robandwend/rook-180-extended/UserMods/RobandWend/12864DisplayFront/image1.JPG

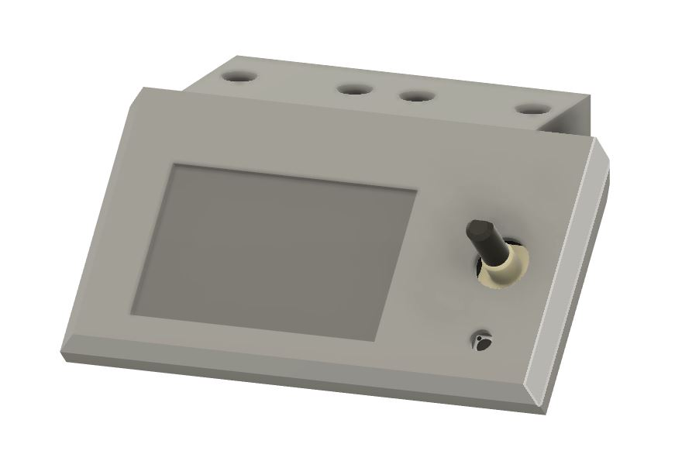
UserMods/RobandWend/12864DisplayFront/image1.JPG
