robandwend/rook-180-extended/UserMods/RobandWend/12864DisplayFront/image2.JPG

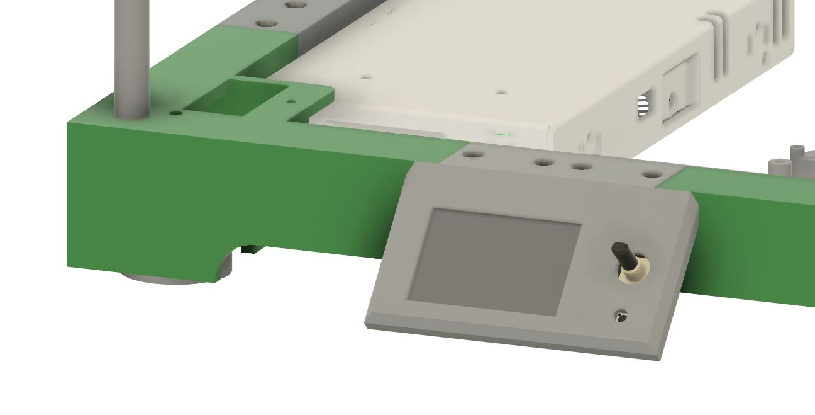
UserMods/RobandWend/12864DisplayFront/image2.JPG
