robandwend/rook-180-extended/UserMods/RobandWend/Photos/ClipGrabPoints.JPG

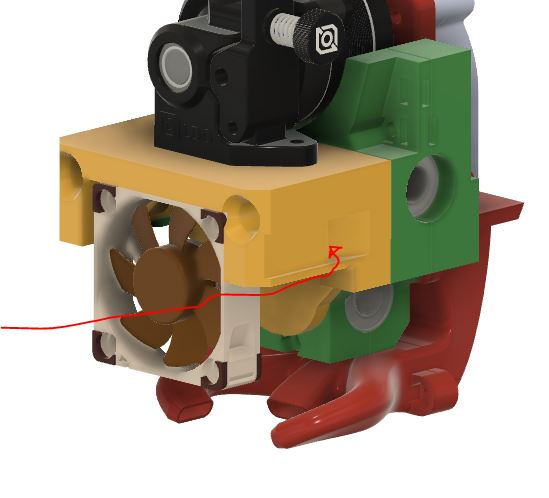
UserMods/RobandWend/Photos/ClipGrabPoints.JPG
