robandwend/rook-180-extended/UserMods/RobandWend/Multi_Hotend/STL/ReplacementArmPart1.stl

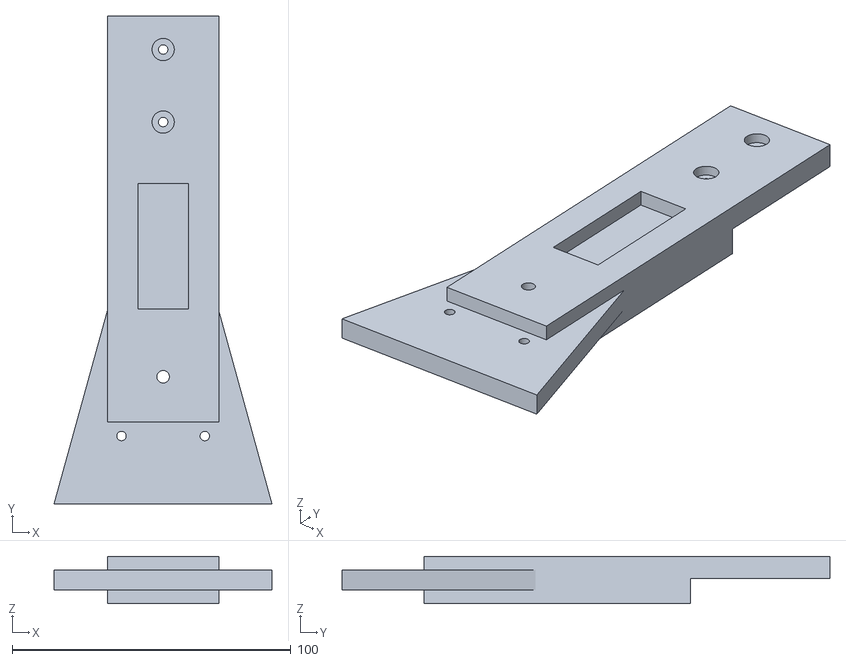
[picture p39: CAD file, 2023-02-05]
UserMods/RobandWend/Multi_Hotend/STL/ReplacementArmPart1.stl
78.1 x 174.9 x 17.0
