robandwend/rook-180-extended/UserMods/RobandWend/Planetery Gear/cover.stl

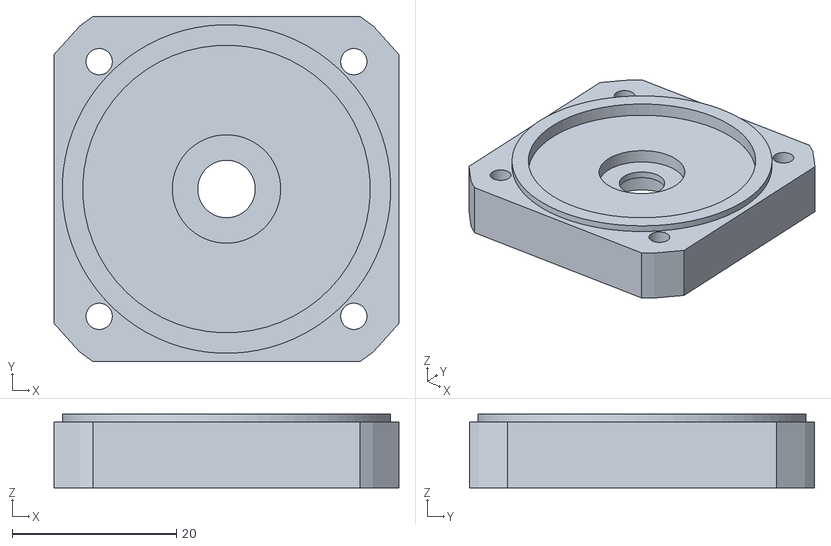
[picture p40: CAD file, 2023-02-15]
UserMods/RobandWend/Planetery Gear/cover.stl
42.0 x 42.0 x 9.00
