robandwend/rook-180-extended/UserMods/RobandWend/Steps/OrbiterWireMount.stl

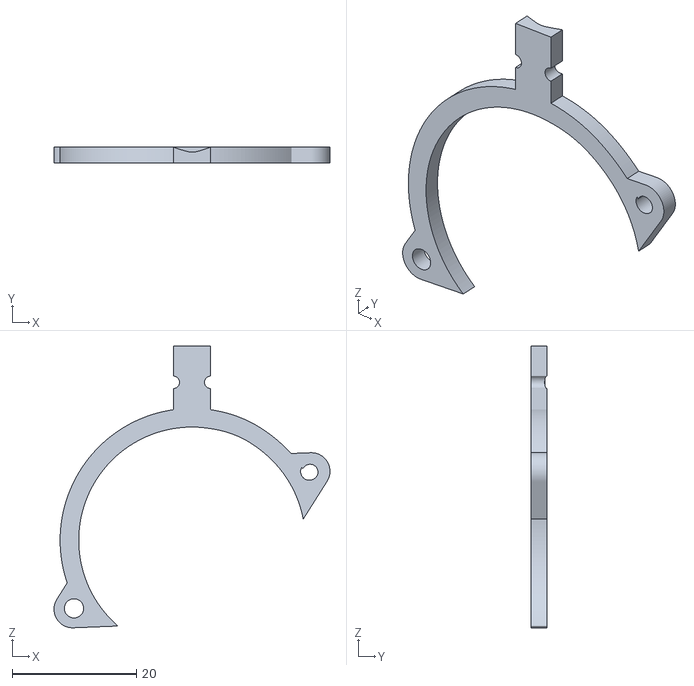
[picture p41: CAD file, 2023-03-21]
UserMods/RobandWend/Steps/OrbiterWireMount.stl
44.4 x 2.50 x 45.3
