robandwend/rook-180-extended/UserMods/RobandWend/Planetery Gear/sun.stl

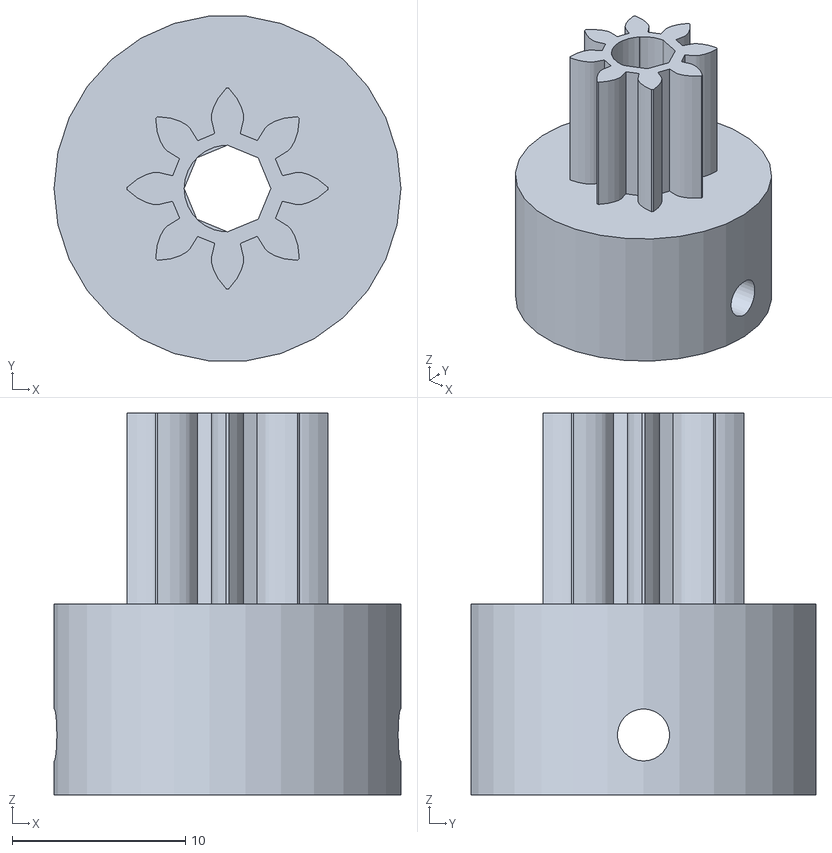
[picture p42: CAD file, 2023-02-15]
UserMods/RobandWend/Planetery Gear/sun.stl
20.0 x 19.9 x 22.0
