robandwend/rook-180-extended/UserMods/RobandWend/Steps/Brace with Raspberry Pi.stl

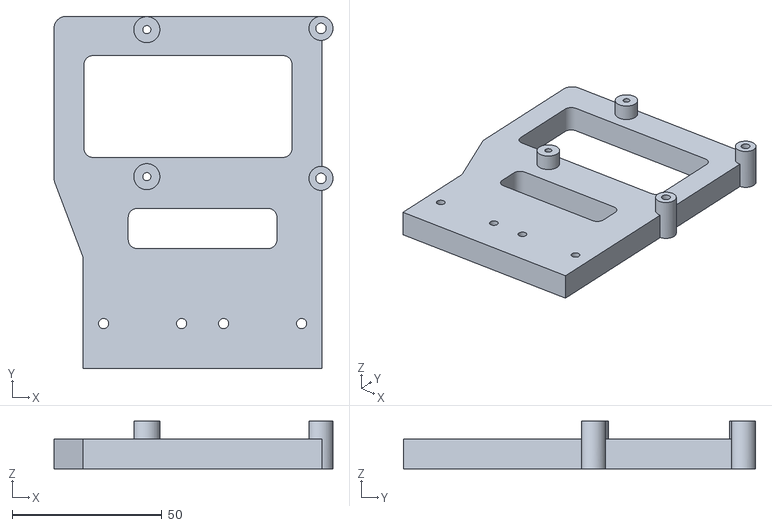
[picture p43: CAD file, 2023-03-21]
UserMods/RobandWend/Steps/Brace with Raspberry Pi.stl
93.0 x 117.4 x 16.0
