robandwend/rook-180-extended/UserMods/RobandWend/Multi_Hotend/STL/2xBottomExtension.stl

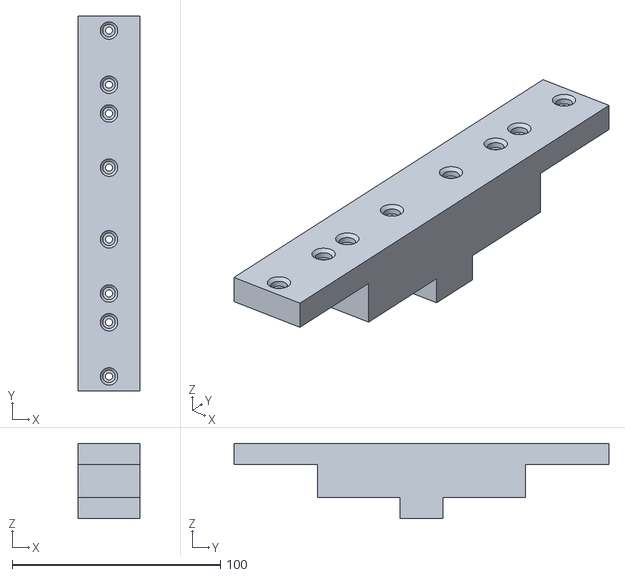
[picture p44: CAD file, 2023-02-05]
UserMods/RobandWend/Multi_Hotend/STL/2xBottomExtension.stl
30.0 x 180.0 x 36.1
