robandwend/rook-180-extended/UserMods/RobandWend/Planetery Gear/planet.stl

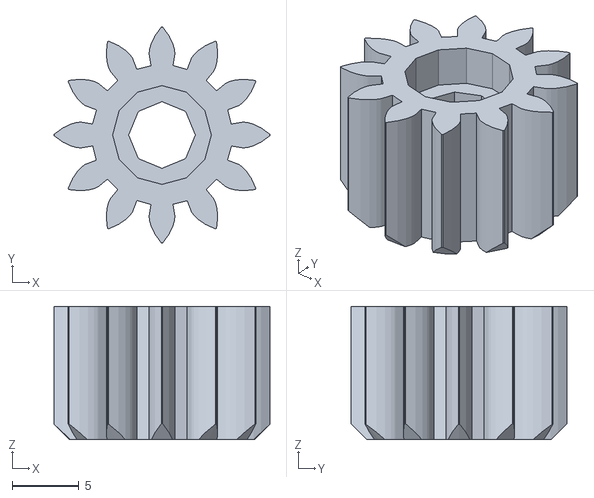
[picture p45: CAD file, 2023-02-15]
UserMods/RobandWend/Planetery Gear/planet.stl
16.2 x 16.2 x 10.0
