robandwend/rook-180-extended/UserMods/RobandWend/Steps/ServoHanger.stl

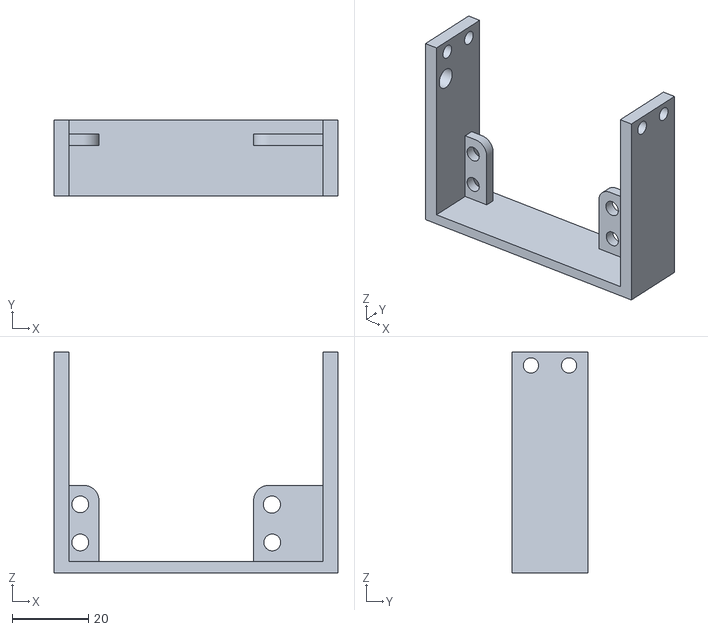
[picture p46: CAD file, 2023-03-21]
UserMods/RobandWend/Steps/ServoHanger.stl
74.6 x 20.0 x 58.0
