robandwend/rook-180-extended/UserMods/RobandWend/Multi_Hotend/STL/2xTopExtension.stl

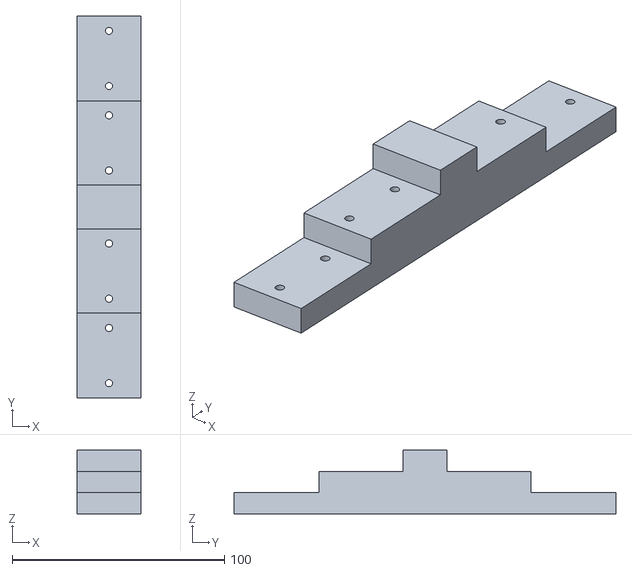
[picture p47: CAD file, 2023-02-05]
UserMods/RobandWend/Multi_Hotend/STL/2xTopExtension.stl
30.0 x 180.0 x 30.0
