robandwend/rook-180-extended/UserMods/RobandWend/Planetery Gear/carrier.stl

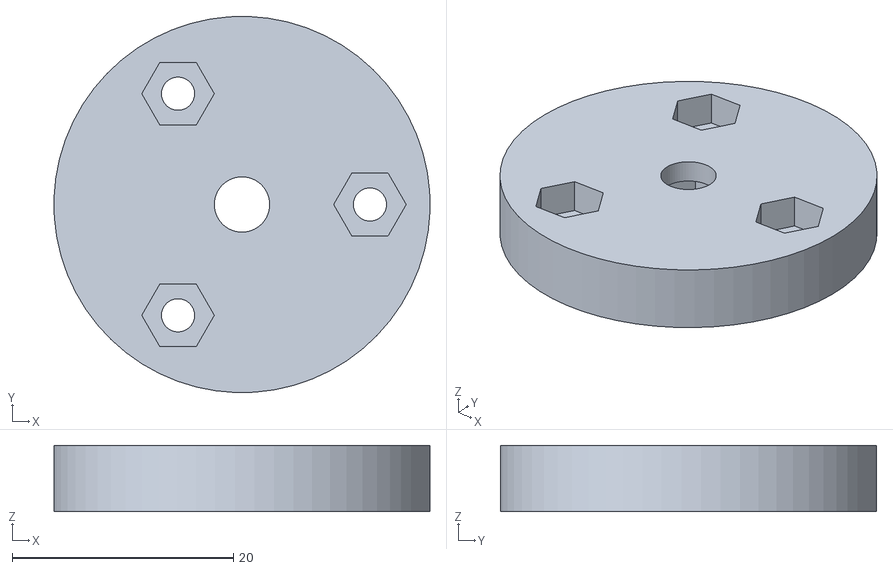
[picture p48: CAD file, 2023-02-15]
UserMods/RobandWend/Planetery Gear/carrier.stl
34.0 x 34.0 x 6.00
