robandwend/rook-180-extended/UserMods/RobandWend/Steps/GrabberHousing.stl

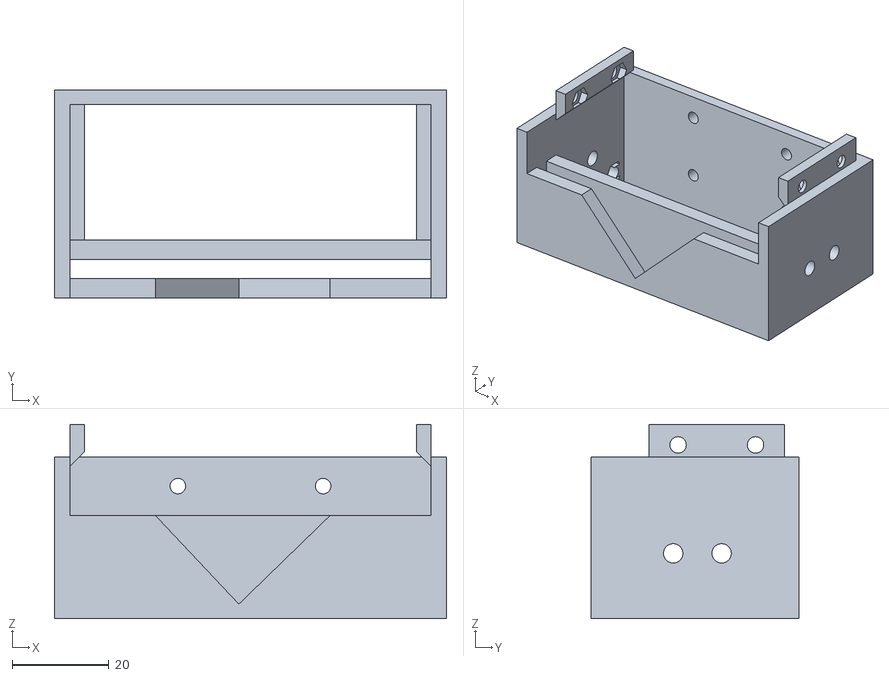
[picture p49: CAD file, 2023-03-21]
UserMods/RobandWend/Steps/GrabberHousing.stl
81.0 x 43.0 x 40.1
