robandwend/rook-180-extended/UserMods/RobandWend/Steps/HorseShoeBrace200mm.stl

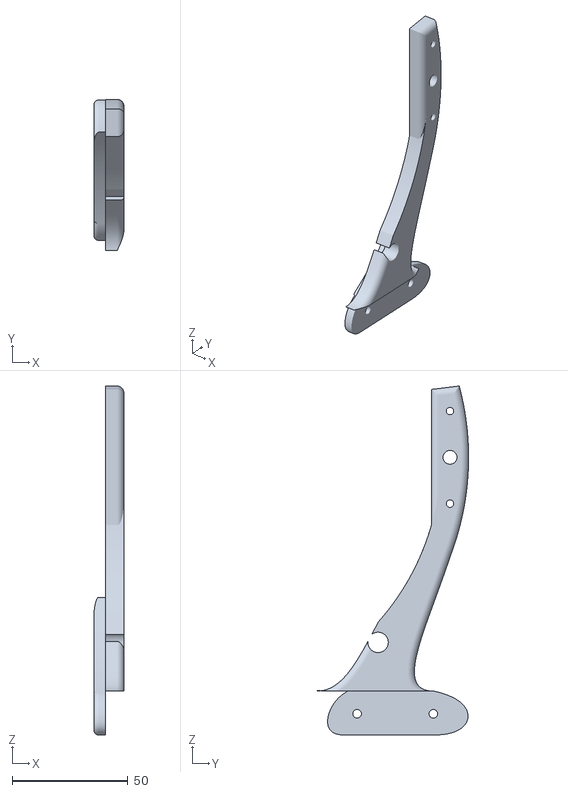
[picture p50: CAD file, 2023-03-21]
UserMods/RobandWend/Steps/HorseShoeBrace200mm.stl
13.0 x 65.3 x 150.7
