robandwend/rook-180-extended/UserMods/RobandWend/Steps/TopServoMount.stl

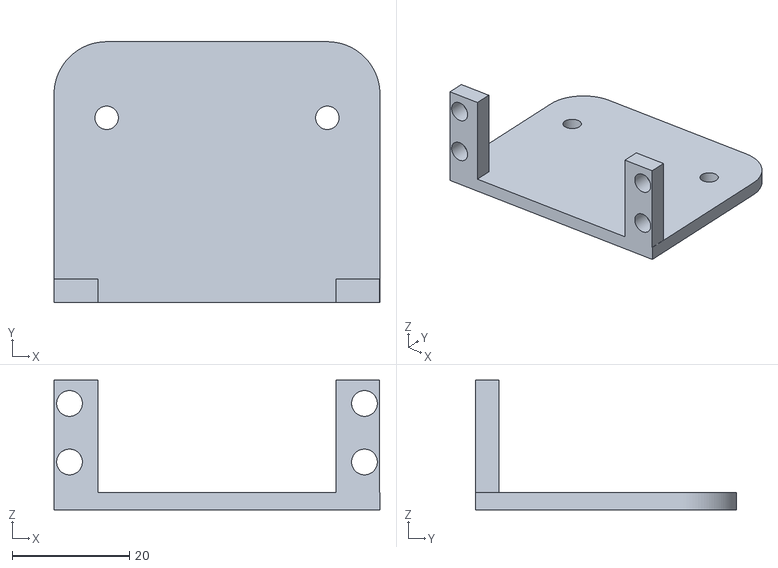
[picture p51: CAD file, 2023-03-21]
UserMods/RobandWend/Steps/TopServoMount.stl
55.7 x 44.5 x 22.2
