robandwend/rook-180-extended/UserMods/RobandWend/Steps/5050 TO 4040 Fan Converter.stl

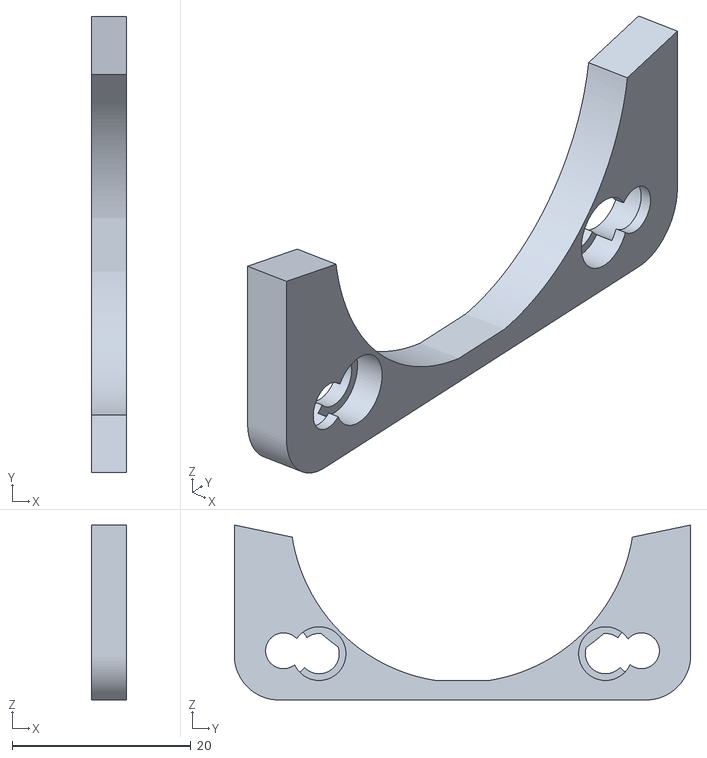
[picture p52: CAD file, 2023-03-21]
UserMods/RobandWend/Steps/5050 TO 4040 Fan Converter.stl
3.95 x 51.0 x 19.6
