robandwend/rook-180-extended/UserMods/RobandWend/Steps/5015_Adapter.stl

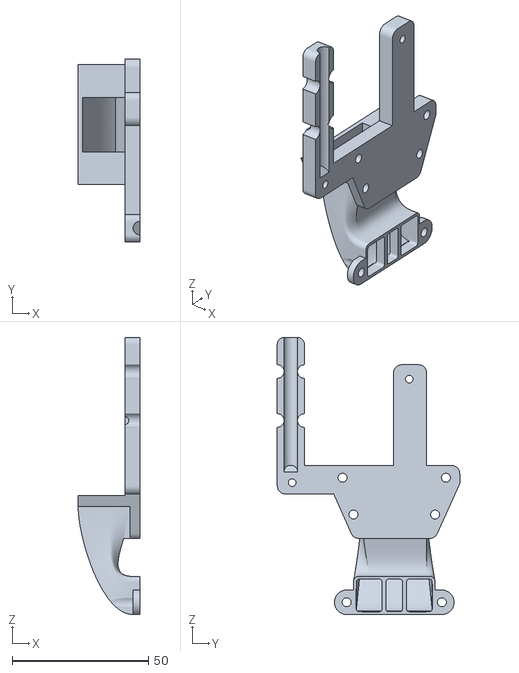
[picture p53: CAD file, 2023-03-21]
UserMods/RobandWend/Steps/5015_Adapter.stl
22.7 x 67.1 x 101.8
