robandwend/rook-180-extended/UserMods/RobandWend/Steps/ExternalSpoolHolder-95mm.stl

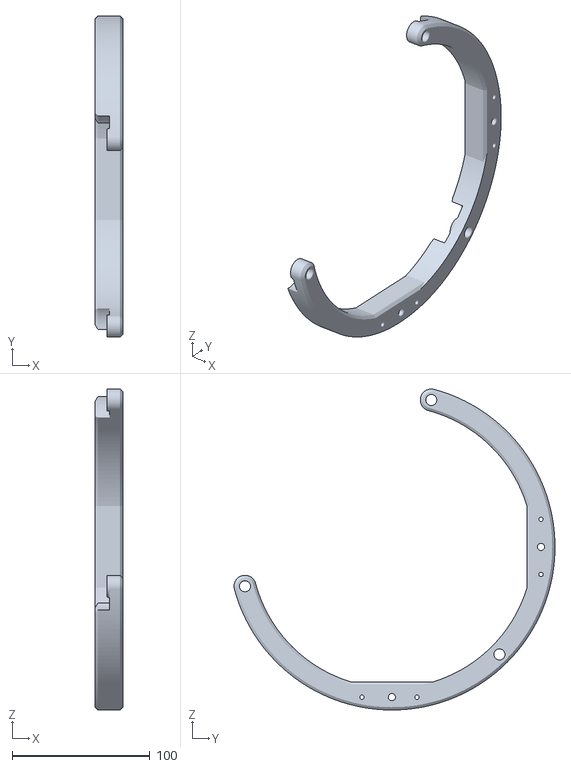
[picture p54: CAD file, 2023-03-21]
UserMods/RobandWend/Steps/ExternalSpoolHolder-95mm.stl
20.0 x 233.2 x 233.2
