robandwend/rook-180-extended/UserMods/RobandWend/Steps/BLTouchStrengthener.stl

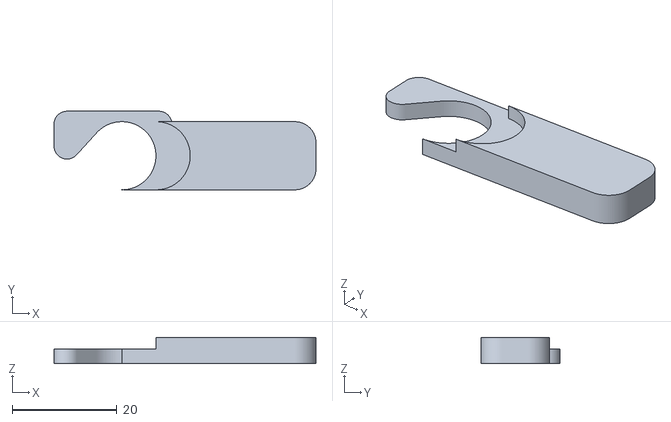
[picture p55: CAD file, 2023-03-21]
UserMods/RobandWend/Steps/BLTouchStrengthener.stl
50.0 x 15.0 x 5.00
