robandwend/rook-180-extended/UserMods/RobandWend/Steps/Z-Endstop.stp

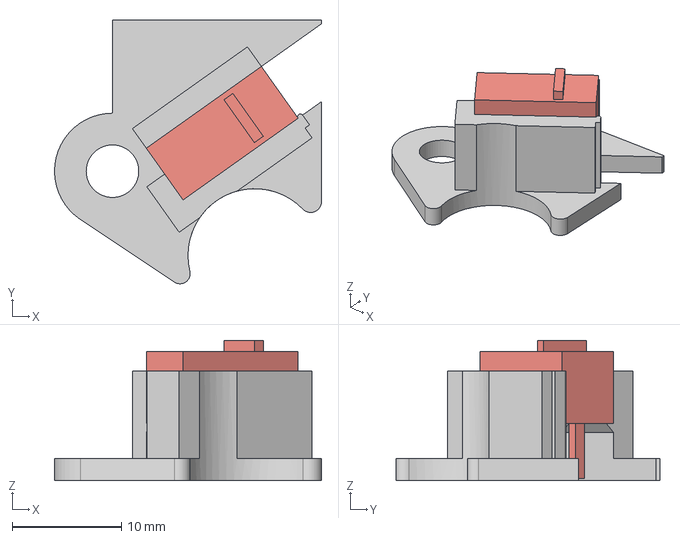
[picture p56: CAD file, 2023-03-21]
UserMods/RobandWend/Steps/Z-Endstop.stp
24.4 x 24.1 x 12.8 mm
