robandwend/rook-180-extended/UserMods/RobandWend/Steps/HarnessClip.stl

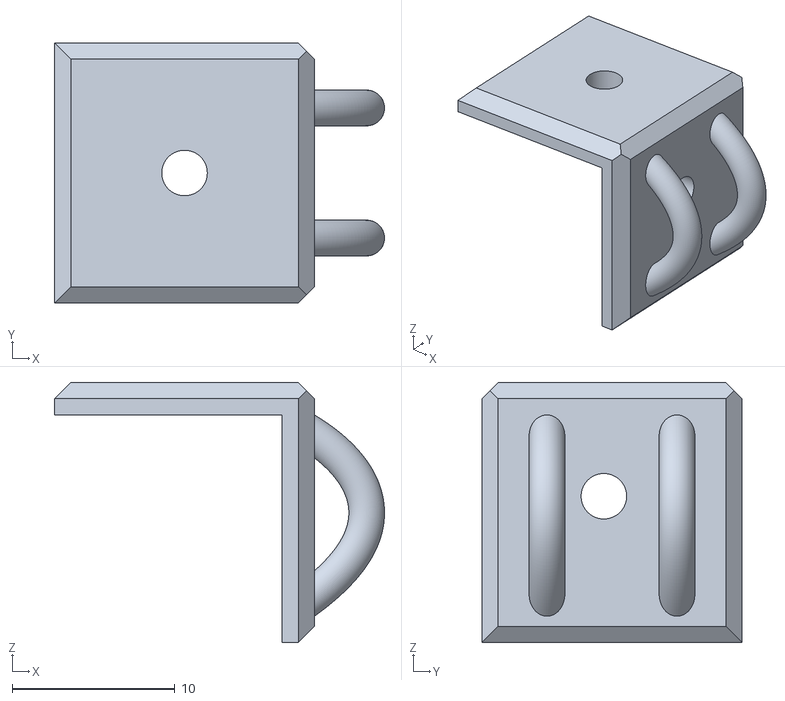
[picture p57: CAD file, 2023-03-21]
UserMods/RobandWend/Steps/HarnessClip.stl
20.3 x 16.0 x 16.0
