robandwend/rook-180-extended/UserMods/RobandWend/Steps/PushOpenBarWithPullback (HB Harness room).stl

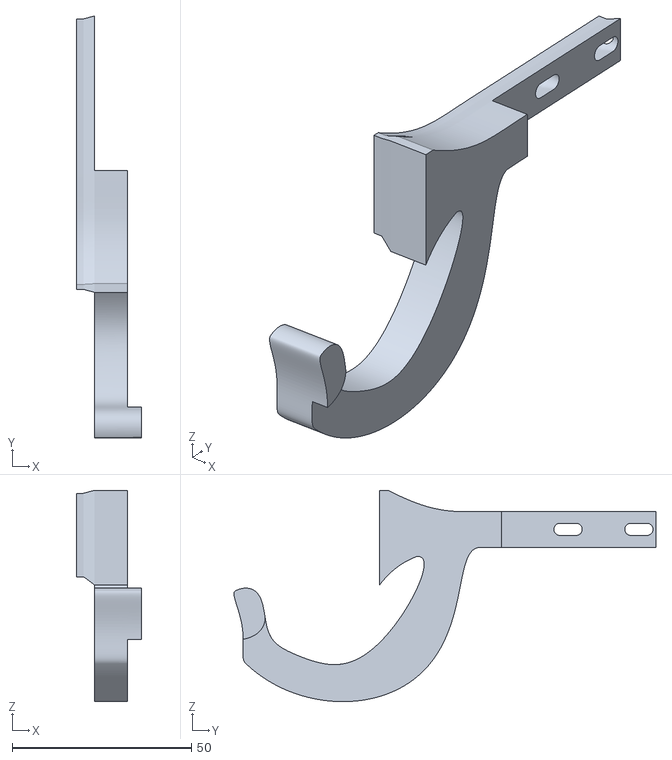
[picture p58: CAD file, 2023-03-21]
UserMods/RobandWend/Steps/PushOpenBarWithPullback (HB Harness room).stl
18.2 x 117.6 x 58.9
