robandwend/rook-180-extended/UserMods/RobandWend/Steps/GrabberHanger(0).stl

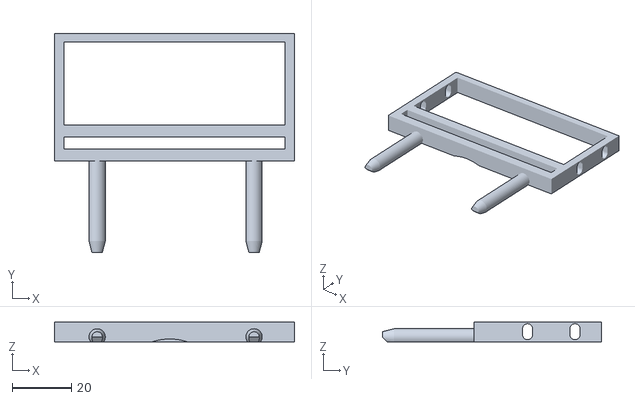
[picture p59: CAD file, 2023-02-15]
UserMods/RobandWend/Steps/GrabberHanger(0).stl
81.0 x 74.0 x 6.70
