robandwend/rook-180-extended/UserMods/RobandWend/Steps/Grabbers.stl

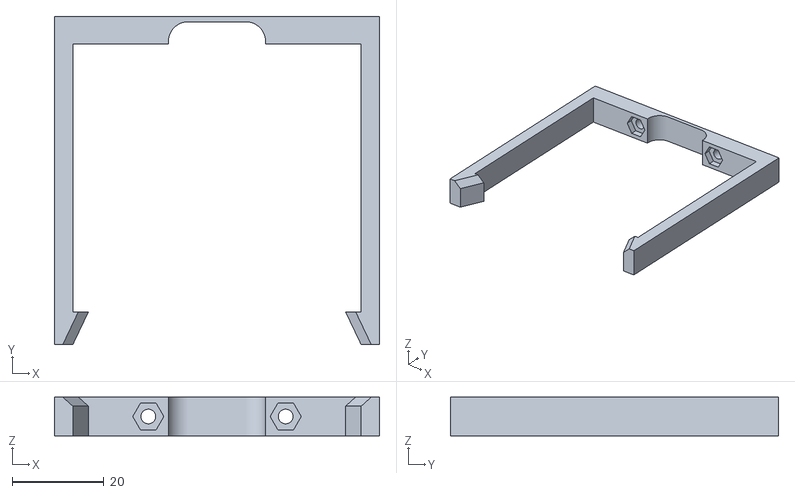
[picture p60: CAD file, 2023-02-15]
UserMods/RobandWend/Steps/Grabbers.stl
71.0 x 71.7 x 8.50
