robandwend/rook-180-extended/UserMods/RobandWend/Steps/ExtruderMount.stl

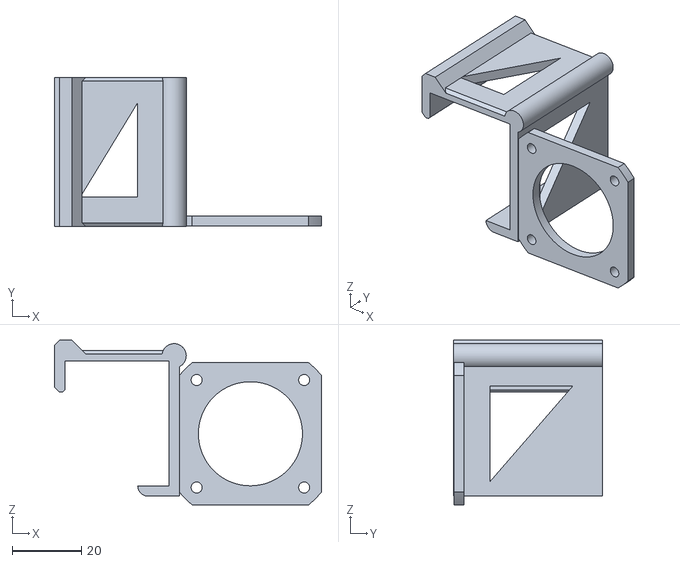
[picture p61: CAD file, 2023-02-15]
UserMods/RobandWend/Steps/ExtruderMount.stl
77.0 x 43.0 x 47.5
