robandwend/rook-180-extended/UserMods/RobandWend/Steps/GrabberTest1.stl

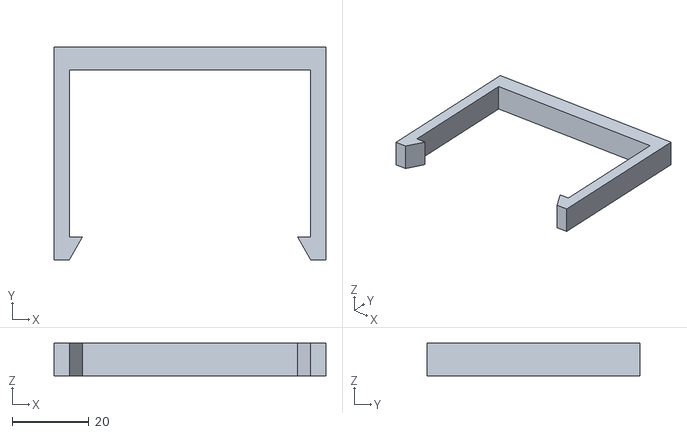
[picture p62: CAD file, 2023-02-15]
UserMods/RobandWend/Steps/GrabberTest1.stl
71.0 x 55.5 x 8.50
