robandwend/rook-180-extended/UserMods/RobandWend/Steps/FrontPart.stl

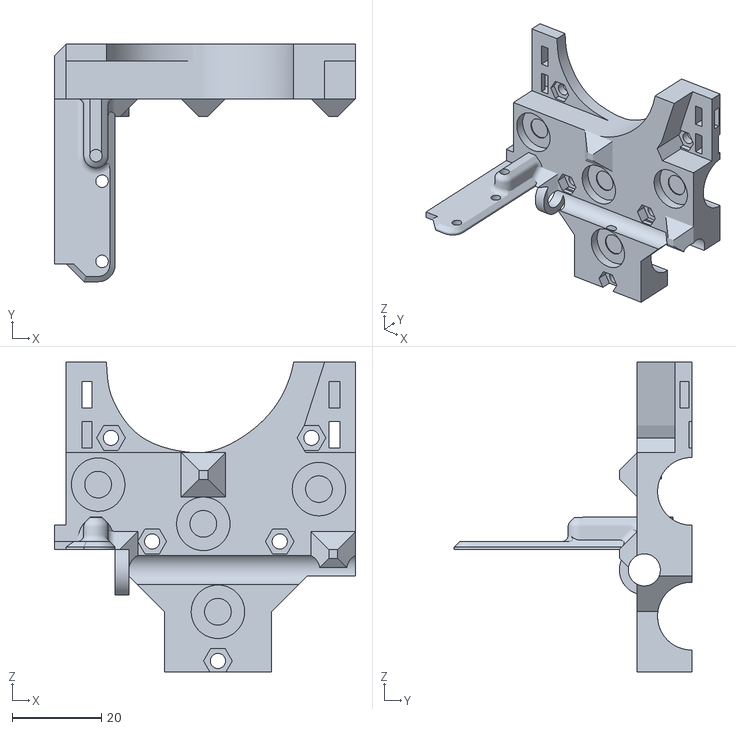
[picture p63: CAD file, 2023-02-15]
UserMods/RobandWend/Steps/FrontPart.stl
67.6 x 53.3 x 69.5
