robandwend/rook-180-extended/UserMods/RobandWend/Steps/PushoffBarCap.stl

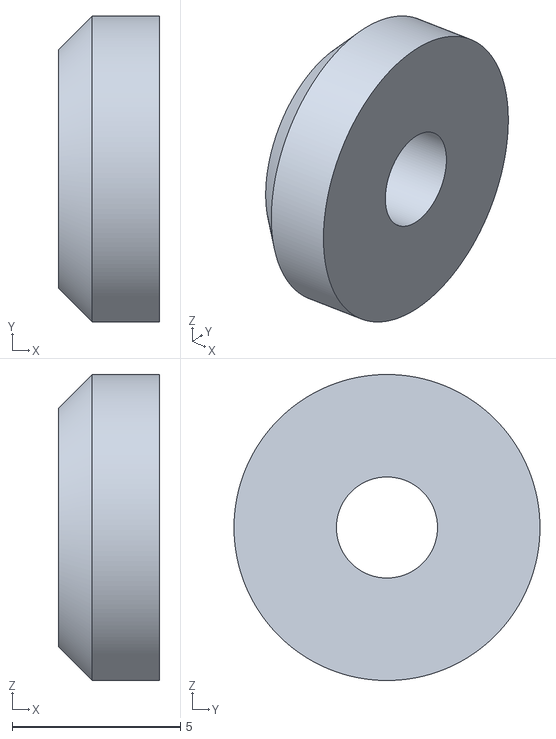
[picture p64: CAD file, 2023-02-15]
UserMods/RobandWend/Steps/PushoffBarCap.stl
3.00 x 9.08 x 9.08
