robandwend/rook-180-extended/UserMods/RobandWend/Steps/BarSpreader.stl

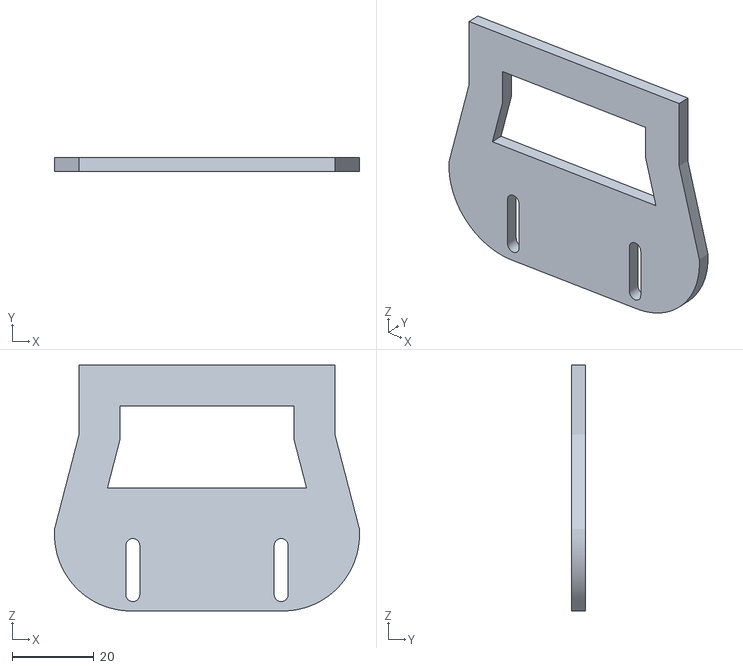
[picture p65: CAD file, 2023-02-15]
UserMods/RobandWend/Steps/BarSpreader.stl
74.6 x 3.30 x 60.1
