robandwend/rook-180-extended/UserMods/RobandWend/Steps/Foot.stl

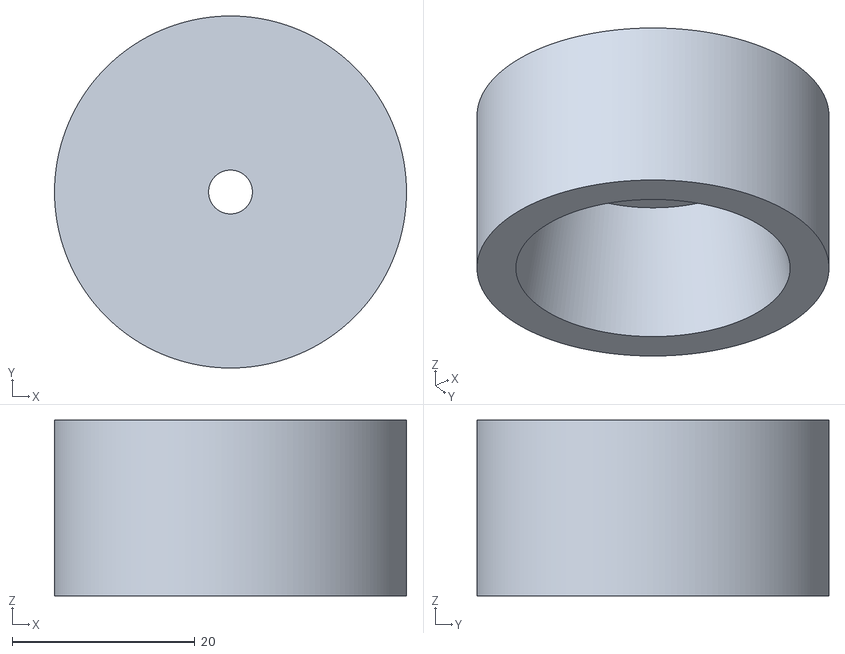
[picture p66: CAD file, 2023-02-15]
UserMods/RobandWend/Steps/Foot.stl
38.5 x 38.5 x 19.2
