robandwend/rook-180-extended/UserMods/RobandWend/Steps/RearMountLeft.stl

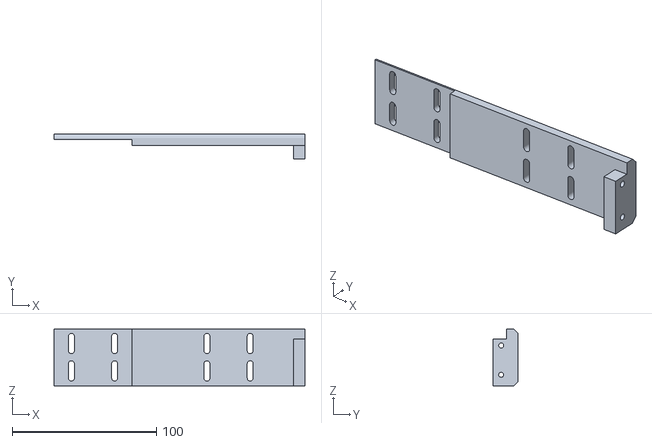
[picture p67: CAD file, 2023-02-15]
UserMods/RobandWend/Steps/RearMountLeft.stl
174.1 x 17.7 x 39.5
