robandwend/rook-180-extended/UserMods/RobandWend/Steps/PushOpenBar.stl

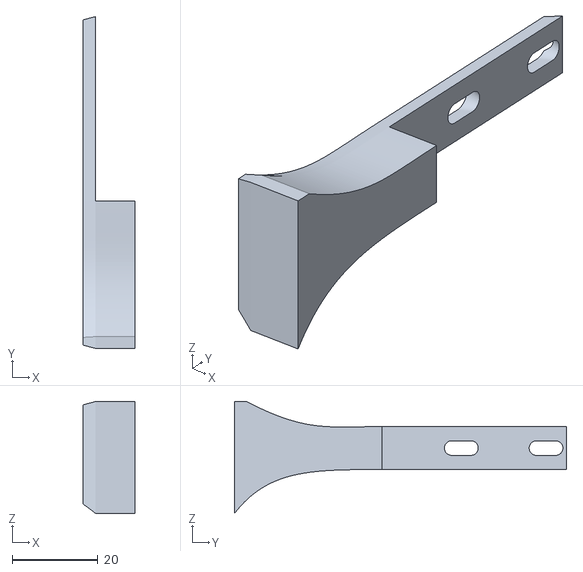
[picture p68: CAD file, 2023-02-15]
UserMods/RobandWend/Steps/PushOpenBar.stl
12.2 x 77.4 x 26.1
