robandwend/rook-180-extended/UserMods/RobandWend/Steps/PushOpenBarWithPullback.stl

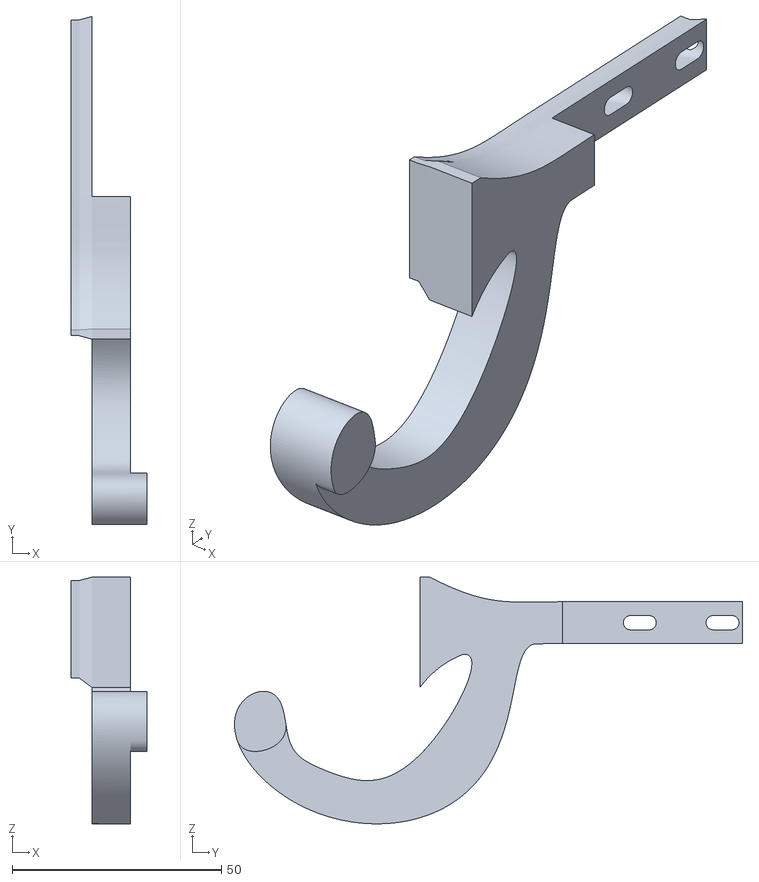
[picture p69: CAD file, 2023-02-15]
UserMods/RobandWend/Steps/PushOpenBarWithPullback.stl
18.2 x 121.2 x 58.9
