robandwend/rook-180-extended/UserMods/RobandWend/Steps/PushoffBar.stl

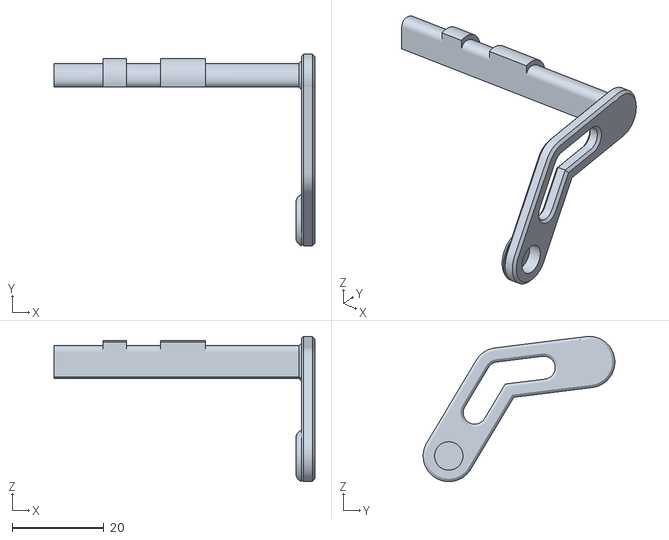
[picture p70: CAD file, 2023-02-15]
UserMods/RobandWend/Steps/PushoffBar.stl
57.0 x 41.8 x 31.7
