robandwend/rook-180-extended/UserMods/RobandWend/Steps/RearPart.stl

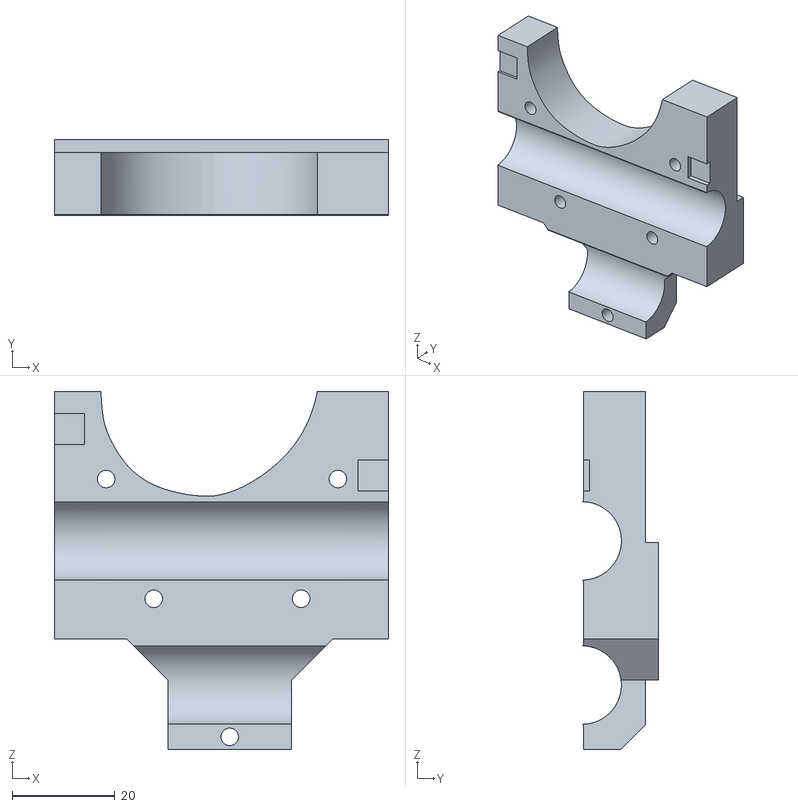
[picture p71: CAD file, 2023-02-05]
UserMods/RobandWend/Steps/RearPart.stl
65.0 x 14.7 x 69.5
