robandwend/rook-180-extended/UserMods/RobandWend/Steps/Braces with MonsterBoard Attachment.stl

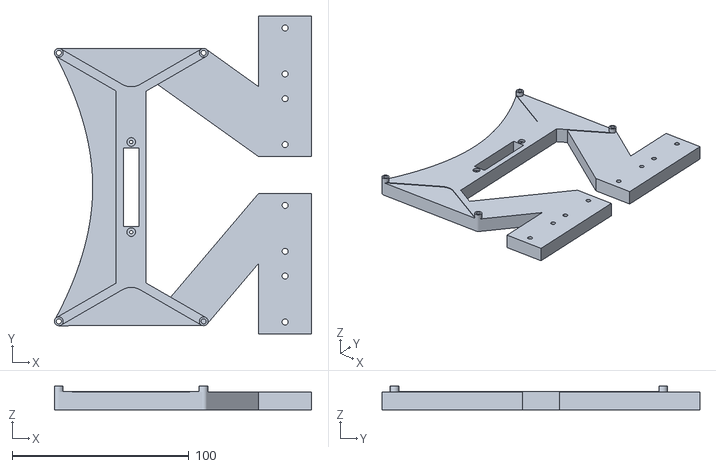
[picture p72: CAD file, 2023-02-05]
UserMods/RobandWend/Steps/Braces with MonsterBoard Attachment.stl
145.6 x 180.0 x 13.4
