robandwend/rook-180-extended/UserMods/RobandWend/Steps/BodyTopFrontRight-2mmExtraRod.stl

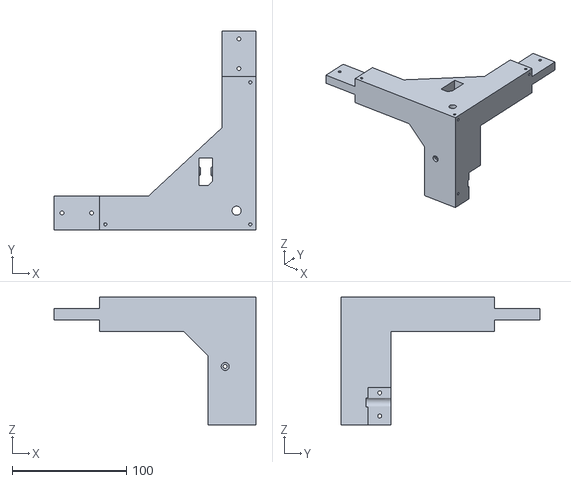
[picture p73: CAD file, 2023-02-05]
UserMods/RobandWend/Steps/BodyTopFrontRight-2mmExtraRod.stl
177.0 x 174.5 x 112.0
