robandwend/rook-180-extended/UserMods/RobandWend/Steps/Monster V8 Motherboard bracket.STL

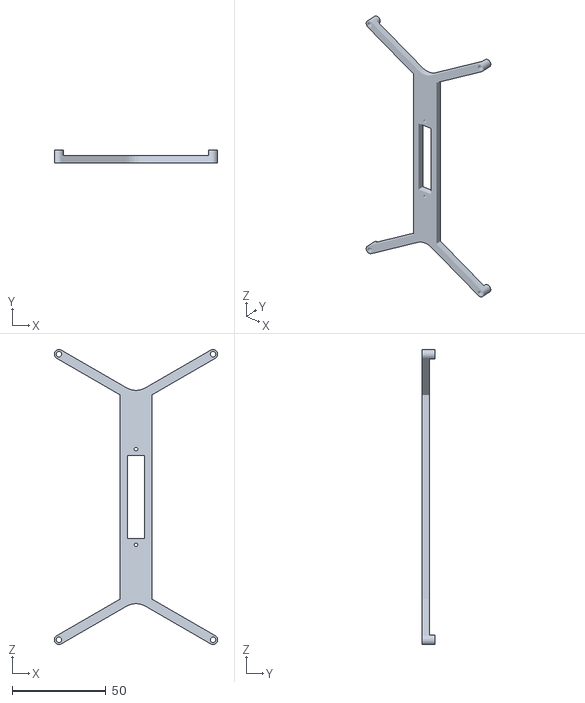
[picture p74: CAD file, 2023-02-05]
UserMods/RobandWend/Steps/Monster V8 Motherboard bracket.STL
87.0 x 7.00 x 157.0
