robandwend/rook-180-extended/UserMods/RobandWend/Steps/PowerSupplyCover.step

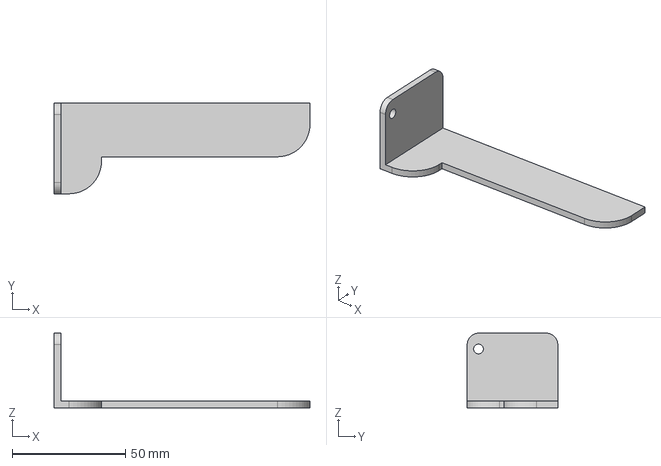
[picture p75: CAD file, 2023-02-05]
UserMods/RobandWend/Steps/PowerSupplyCover.step
113.0 x 40.0 x 33.0 mm
