robandwend/rook-180-extended/UserMods/RobandWend/Steps/Brace with OrangePiPC.stl

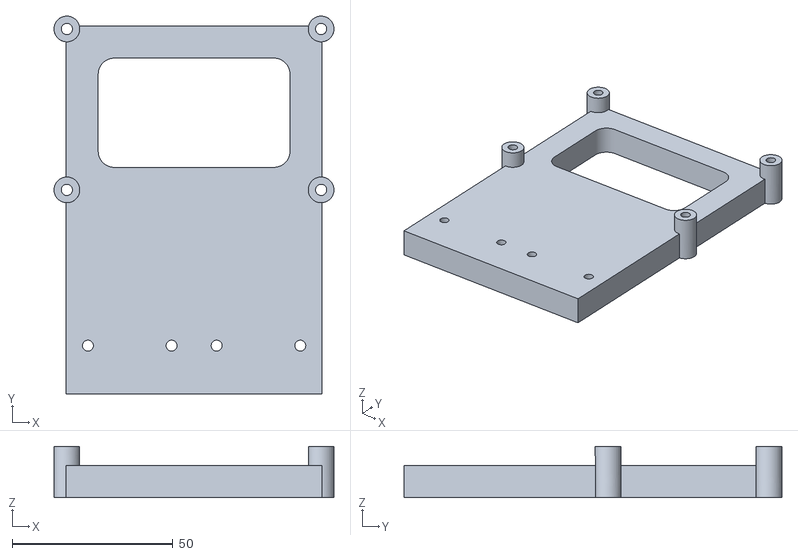
[picture p76: CAD file, 2023-02-05]
UserMods/RobandWend/Steps/Brace with OrangePiPC.stl
87.0 x 117.4 x 16.0
